HedronUser/sensing/Rpi/Recordings/Frequency Analsysi Screen Shot 2018-02-06 at 11.28.25 AM.png

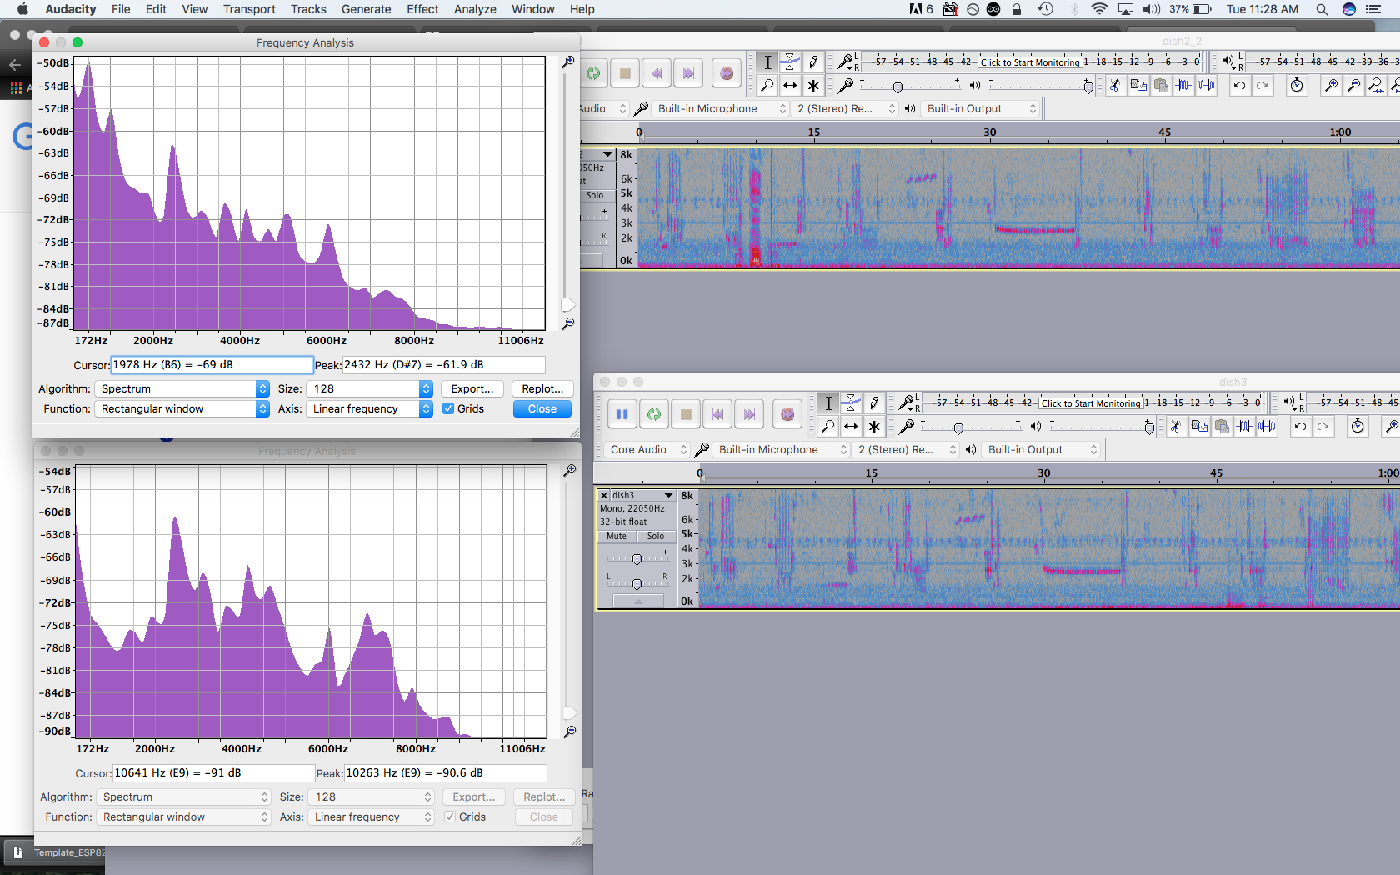
Rpi/Recordings/Frequency Analsysi Screen Shot 2018-02-06 at 11.28.25 AM.png
