HedronUser/sensing/Rpi/Recordings/Frequency analysis Screen Shot 2018-02-06 at 11.30.29 AM.png

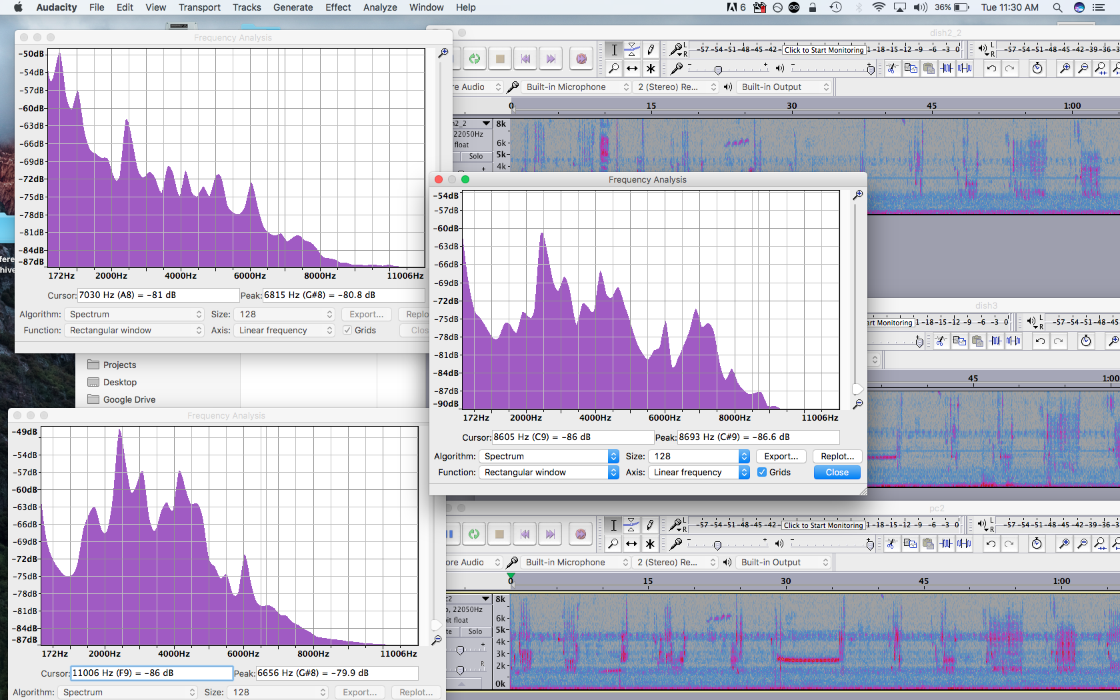
Rpi/Recordings/Frequency analysis Screen Shot 2018-02-06 at 11.30.29 AM.png
