HedronUser/sensing/Rpi/Recordings/IMG_1986.JPG

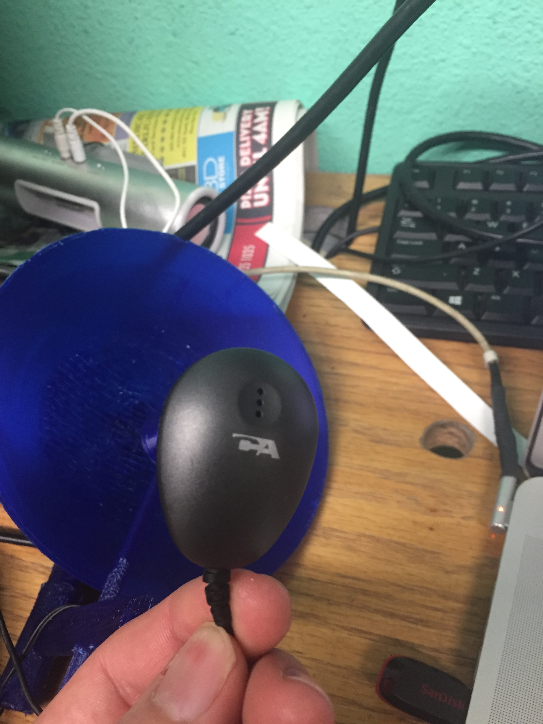
Rpi/Recordings/IMG_1986.JPG
