HedronUser/sensing/Rpi/Recordings/IMG_1987.JPG

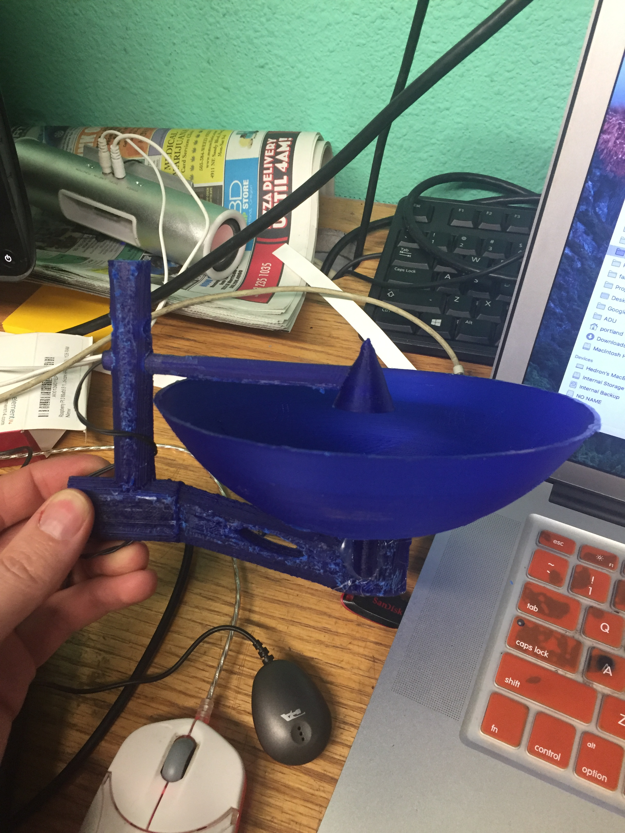
Rpi/Recordings/IMG_1987.JPG
