HedronUser/sensing/Rpi/Recordings/IMG_1988.JPG

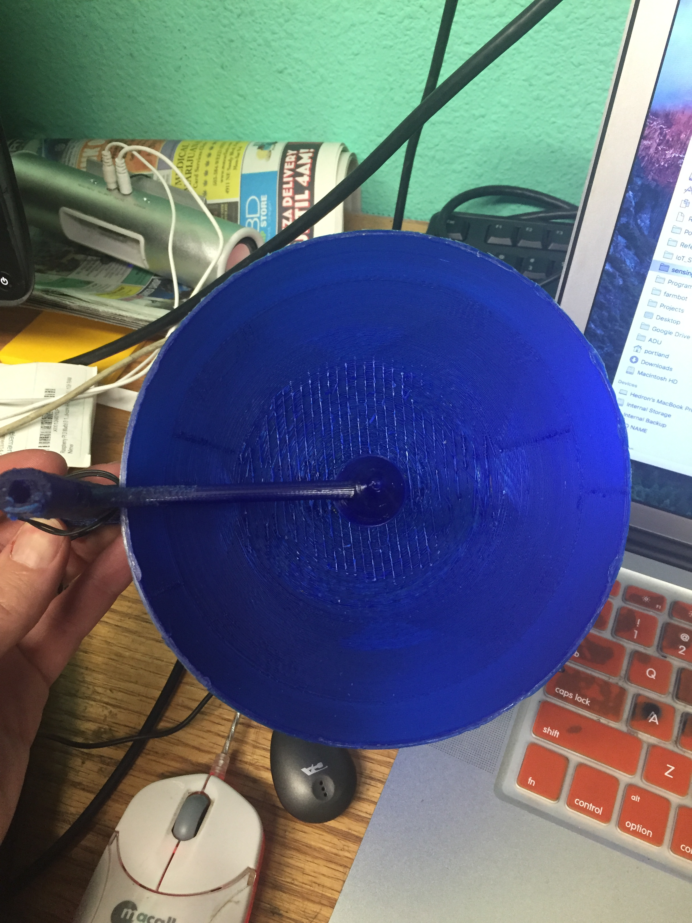
Rpi/Recordings/IMG_1988.JPG
