HedronUser/sensing/Rpi/Recordings/IMG_1989.JPG

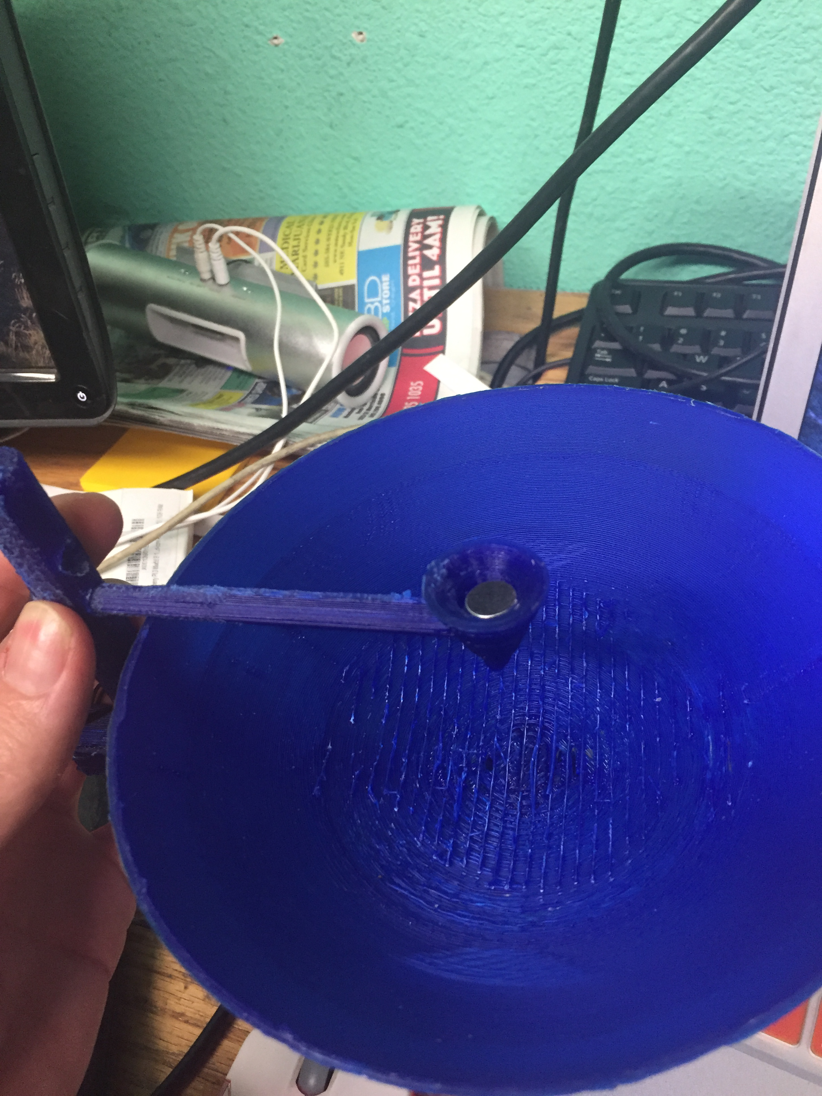
Rpi/Recordings/IMG_1989.JPG
