HedronUser/sensing/Rpi/Recordings/Volume comparison Screen Shot 2018-02-06 at 11.45.52 AM.png

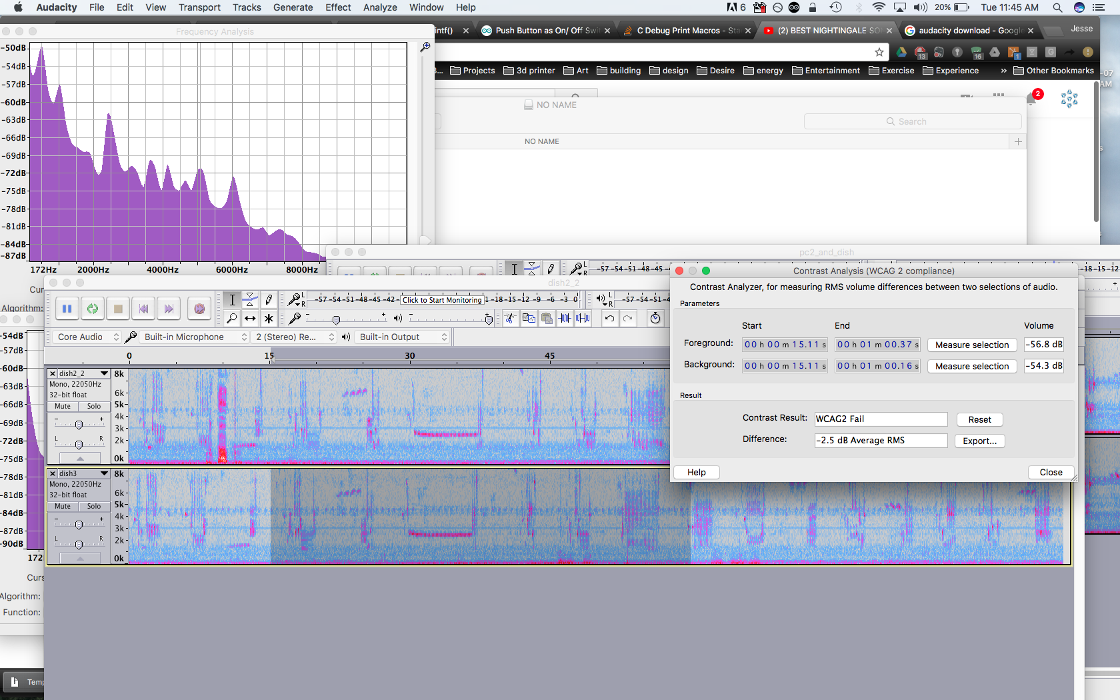
Rpi/Recordings/Volume comparison Screen Shot 2018-02-06 at 11.45.52 AM.png
