HedronUser/sensing/Rpi/Recordings/Waveform comparison Screen Shot 2018-02-06 at 11.22.07 AM.png

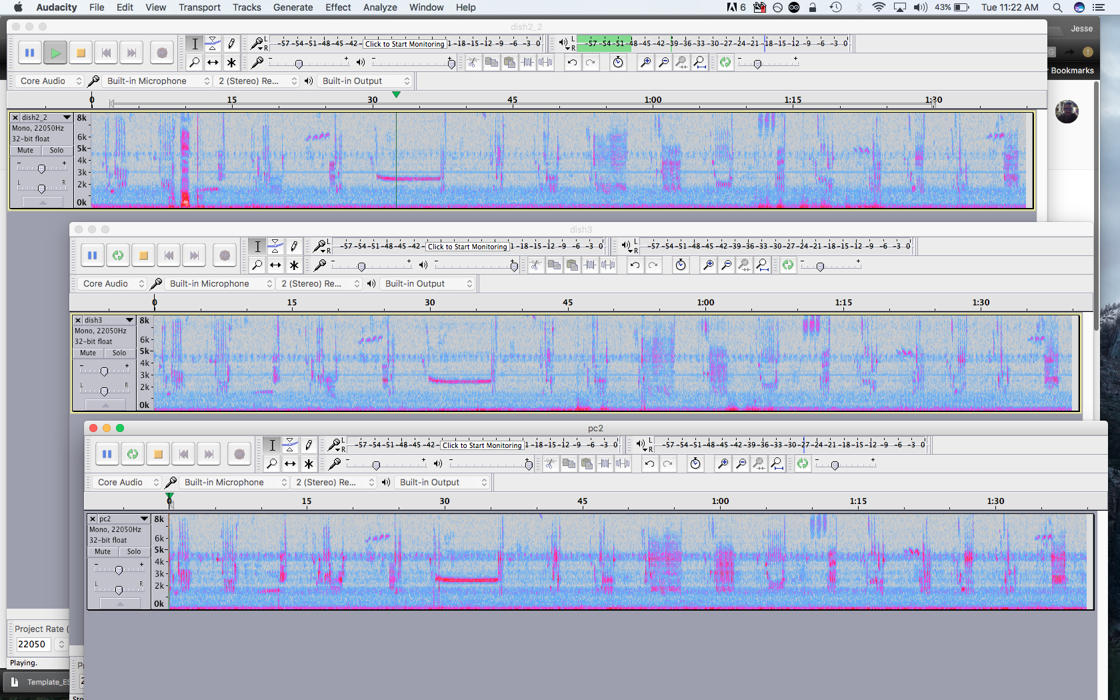
Rpi/Recordings/Waveform comparison Screen Shot 2018-02-06 at 11.22.07 AM.png
